omarmuoz-lab/Smart-Meter/Firmware/ADE9000_Main_Wifi_SD_Real_Time_Event_V3_mqtt_complete/ADE9000CalibrationInputs.h

/*Calibration Procedure*/
/*Setup ADE9000. Set the desired configuration registers in ADE9000API.h file.*/
/*Fill the user inputs, transfer function and conversion constants*/
/*Follow directions shown on serial monitor */

/*User Inputs*/
#define NOMINAL_INPUT_VOLTAGE 127.2//123.25//124.4//123.15//110       //Nominal Calibrating RMS Voltage on all phases (Vrms)
#define NOMINAL_INPUT_CURRENT 9.96//7.055//10.00//5         //Nominal Calibrating RMS Current on all phases (Irms)
#define MIN_INPUT_VOLTAGE 20.02
#define MIN_INPUT_CURRENT 0.0215//0.0250
#define INPUT_FREQUENCY 60              //Nominal Calibrating frequency. Used to calculate Omega for phase calibration.Ensure ACCMODE register is set to correct frequency
#define CALIBRATION_ANGLE_DEGREES 60  //Calibration Angle in Degrees.Used for phase calibration
#define CALIBRATION2_ANGLE_DEGREES 83//0.12 //Calibration Angle in Degrees.Used for offset calibration

/*Transfer function*/
/****************************************************************************************************************
                  Current Transfer Function
*****************************************************************************************************************
It is the voltage at the ADC input pins per input current(A) (Volts/Amp)
E.g: For a current output current transformer with Turns Ratio of 2500:1. Burden resistor on board = 5.1*2=10.2 Ohm.
Current transfer function= 1/2500*Total Burden = 1/2500*10.2= 0.00408
****************************************************************************************************************/
/****************************************************************************************************************
                  Voltage Transfer Function
*****************************************************************************************************************
It is the voltage at the ADC input pins per input Voltage(V)(Volts/Volts)
E.g. The defaul atteunation factor on board is 801. 
Voltage transfer function = 1/801= 0.001248 ~=0.00125
****************************************************************************************************************/                                  
#define CURRENT_TRANSFER_FUNCTION 0.00357//0.003535//0.00408   //The RMS voltage at the ADC input pins per input RMS current  (V/A).(2500:1-->0.00408 with default burden resistors)
#define VOLTAGE_TRANSFER_FUNCTION  0.000999//0.001248//0.00125 //The RMS voltage at the ADC input pins per input RMS voltage (V/V) 
/****************************************************************************************************************
                  Constants: Do not change 
*****************************************************************************************************************/
#define F_DSP 8000                         //Signal update Rate
#define CALIBRATION_EGY_CFG 0xF011         //Latch after EGYRDY. Sample based accumulation. Read with reset disabled. Accumulation enabled
#define EGYACCTIME 0x1F3F                  //Accumulate for a total of 8000 (EGY_TIME+1) samples.
#define CALIBRATION_ACC_TIME 10            //if EGYACCTIME= 0x1F3F, Accumulation time is 1sec. Change this if EGYACCTIME is changed.

#define CAL_ANGLE_RADIANS(x) (x*3.14159/180)


/****************************************************************************************************************
                  Conversion Constants
*****************************************************************************************************************
If calibration is done with the the calibration sketch, the following conversion constants apply:
If CURRENT_TRANSFER_FUNCTION or VOLTAGE_TRANSFER_FUNCTION are changed, update the conversion constants

CAL_IRMS_CC in uA/code        = 10^6/(CURRENT_TRANSFER_FUNCTION*ADE9000_RMS_FULL_SCALE_CODES*SQRT(2)) 
CAL_VRMS_CC in uV/code        = 10^6/(VOLTAGE_TRANSFER_FUNCTION*ADE9000_RMS_FULL_SCALE_CODES*SQRT(2))
CAL_POWER_CC in mW/code       = 10^3/(CURRENT_TRANSFER_FUNCTION*VOLTAGE_TRANSFER_FUNCTION*ADE9000_WATT_FULL_SCALE_CODES*2)
CAL_ENERGY_CC in uWhr/xTHR_HI code  = 10^6/(CURRENT_TRANSFER_FUNCTION*VOLTAGE_TRANSFER_FUNCTION*ADE9000_WATT_FULL_SCALE_CODES*2*8000*3600*2^-13)

If conversion constants are set correctly, the register codes are converted to physical parameters as:
e.g Channel A Vrms = (AVRMS(register)*CAL_VRMS_CC/10^6)
  Channel A Active Power = (AWATT(register)*CAL_POWER_CC/10^3)  
*****************************************************************************************************************/
#define CAL_IRMS_CC   3.757711//3.795488//3.28849         // (uA/code)
#define CAL_VRMS_CC   13.428442//10.750844//10.73364       // (uV/code)  
#define CAL_POWER_CC  6.772654//5.476715//4.73755         // (mW/code) Applicable for Active, reactive and apparent power
#define CAL_ENERGY_CC 1.926685//1.557821//1.34757         // (uWhr/xTHR_HI code)Applicable for Active, reactive and apparent energy
